FPGA-Computer/STM8-LCDUSB/LCD2USB/LCD.c

/*
 * lcd.c
 *
 * Created: April-08-15, 3:09:59 PM
 *  Author: K. C. Lee
 * Copyright (c) 2017 by K. C. Lee
 
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
 If not, see http://www.gnu.org/licenses/gpl-3.0.en.html 
 */ 
#include "LCD.h"

// minimum delay for 16MHz
uint8_t LCD_X, LCD_Y;

void LCD_Short_Delay(void)
{
		_asm("nop");
		_asm("nop");
		_asm("nop");
		_asm("nop");
		_asm("nop");	
		_asm("nop");		
}

void LCD_WR_High_Nibble(uint8_t Code)
{
	LCD_DATA_PORT->ODR = (uint8_t)((Code>>(4-LCD_DOFFSET))&LCD_DATA);
	LCD_DATA_PORT->DDR |= LCD_DATA;	
	Delay(_LCD_DATABUS_DELAY);
	Set_LCD_E();
	LCD_Short_Delay();	
	Clr_LCD_E();
	LCD_Short_Delay();	
}

void LCD_WR(uint8_t LCD_data)
{ 
  // DDR = Output
  Clr_LCD_RW();
  LCD_WR_High_Nibble((uint8_t)(LCD_data & 0xf0));
  LCD_WR_High_Nibble((uint8_t)(LCD_data << 4));
  // set port back to input  
  LCD_DATA_PORT->DDR &= (uint8_t)~LCD_DATA;
	LCD_Short_Delay();	
 }

uint8_t LCD_RD(void)
{ uint8_t LCD_Data, i;

	Set_LCD_RW();
  Set_LCD_E();
	Delay(_LCD_DATABUS_DELAY);
  LCD_Data = (uint8_t)((LCD_DATA_PORT->IDR & LCD_DATA)<<(4-LCD_DOFFSET));	
	Clr_LCD_E();
	LCD_Short_Delay();   
  Set_LCD_E();
	Delay(_LCD_DATABUS_DELAY);
  LCD_Data |= (uint8_t)((uint8_t)(LCD_DATA_PORT->IDR >>LCD_DOFFSET)&0x0f);
  Clr_LCD_E();
	LCD_Short_Delay();	
  return(LCD_Data);
 }

void LCD_Wait(void)
{ 
  Clr_LCD_RS();
	
  while (LCD_RD() & _LCD_BUSY)
    /* WAIT */ ;
 }

void LCD_Data(uint8_t LCD_Data)
{ 
  LCD_Wait();
  Set_LCD_RS();
  LCD_WR(LCD_Data);
 }

void LCD_Cmd(uint8_t Cmd)
{ 
  LCD_Wait();
  Clr_LCD_RS();
  LCD_WR(Cmd);
 }

void LCD_Cls(void)
{
	LCD_Cmd(_LCD_CLR);	

	LCD_X = LCD_Y = 0;
}

// Power On LCD reset    
void LCD_SetMode(void)
{ 
	LCD_WR_High_Nibble(_LCD_Set8bit);
	Delay(_LCD_INIT_DELAY1);
	
	LCD_WR_High_Nibble(_LCD_Set8bit);
	Delay(_LCD_INIT_DELAY2);
	
	LCD_WR_High_Nibble(_LCD_Set8bit);
	LCD_WR_High_Nibble(_LCD_FuncSetH);

	LCD_Cmd(_LCD_FuncSet);	
	LCD_Cmd(_LCD_ENTRY);
	LCD_Cls();
	LCD_Cmd(_LCD_ON|_LCD_DISPLAY_ON);	
	
	#ifdef LCD_CUSTOM_CHR
	LCD_UserCh();
	#endif
 }

void LCD_Contrast(uint8_t Contrast)
{
	TIM2->CCR3H = 0;
	TIM2->CCR3L = Contrast;
}

//--- LCD2USB don't use these
// Cursor support
void LCD_Moveto(uint8_t X, uint8_t Y)
{ 
	LCD_X = (uint8_t)(X & _LCD_XMASK);
	LCD_Y = (uint8_t)(Y & _LCD_YMASK);
	
	LCD_Cmd((uint8_t)(_LCD_DD|LCD_Addr(LCD_X,LCD_Y)));
 }

void LCD_Ch(uint8_t Ch)
{
	LCD_Data(Ch);
	LCD_X++;
	
	if(LCD_X > _LCD_XMASK)
	{
		LCD_X = 0;
		LCD_Y = 1;
		
		LCD_Moveto(0,1);
	}
 }

#ifdef LCD_CUSTOM_CHR

LCD_CUSTOM_CHR
const uint8_t LCD_CG[]=
{ 
	0,0,0,0,0,0,0,0x1f,
	0,0,0,0,0,0,0x1f,0x1f,
	0,0,0,0,0,0x1f,0x1f,0x1f,
	0,0,0,0,0x1f,0x1f,0x1f,0x1f,
	0,0,0,0x1f,0x1f,0x1f,0x1f,0x1f,
	0,0,0x1f,0x1f,0x1f,0x1f,0x1f,0x1f,
	0,0x1f,0x1f,0x1f,0x1f,0x1f,0x1f,0x1f,
	0x1f,0x1f,0x1f,0x1f,0x1f,0x1f,0x1f,0x1f
};

void LCD_UserCh(void)
{ uint8_t i;

  LCD_Cmd(_LCD_CG);
  
  for(i=0;i<sizeof(LCD_CG);i++)
    LCD_Data(LCD_CG[i]);

  LCD_Cmd(_LCD_DD);  
 }

#endif

void LCD_Puts(char *str)
{
	while(*str)
	  LCD_Ch(*str++);
}
